travisjbeck/focus-dial/Documents/rendering2.png

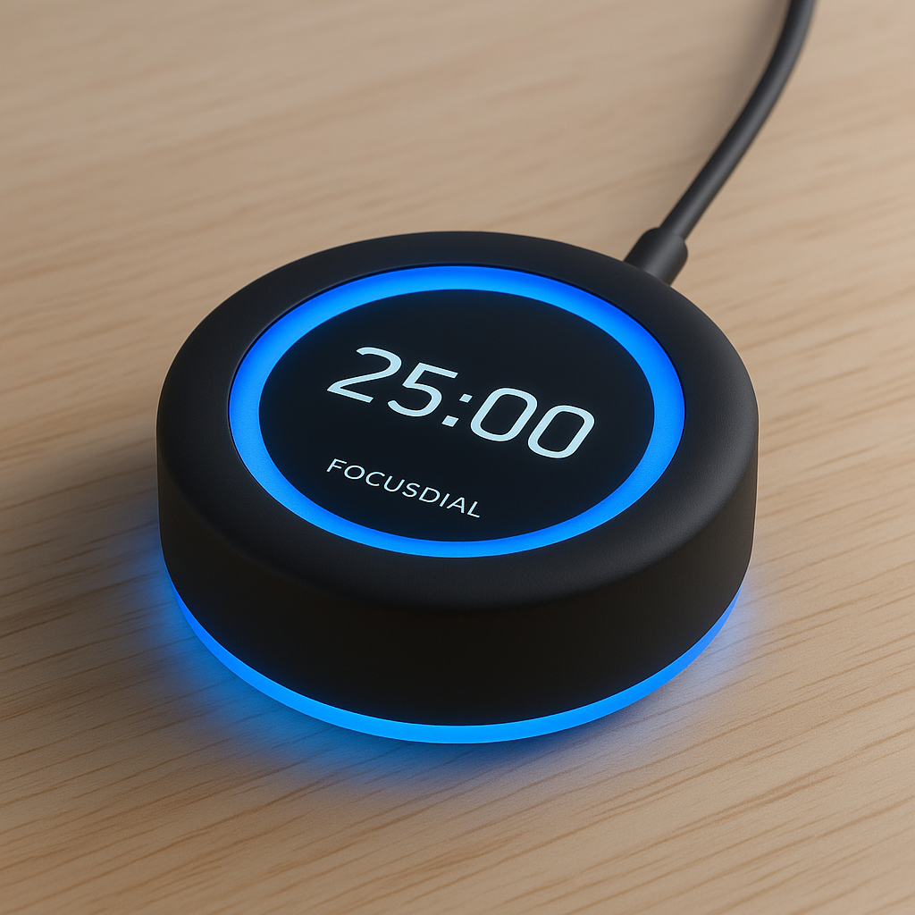
Documents/rendering2.png
