travisjbeck/focus-dial/Documents/rendering3.png

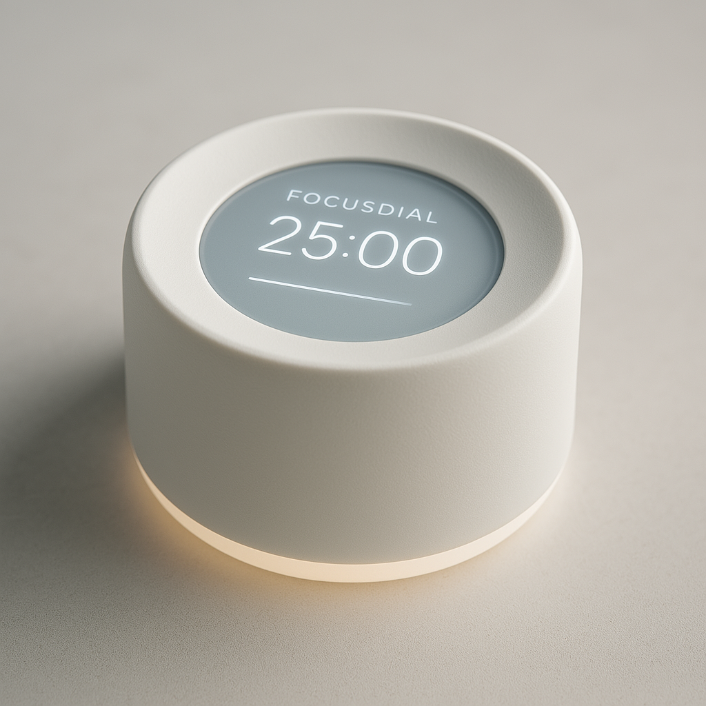
Documents/rendering3.png
