travisjbeck/focus-dial/Documents/rendering4.png

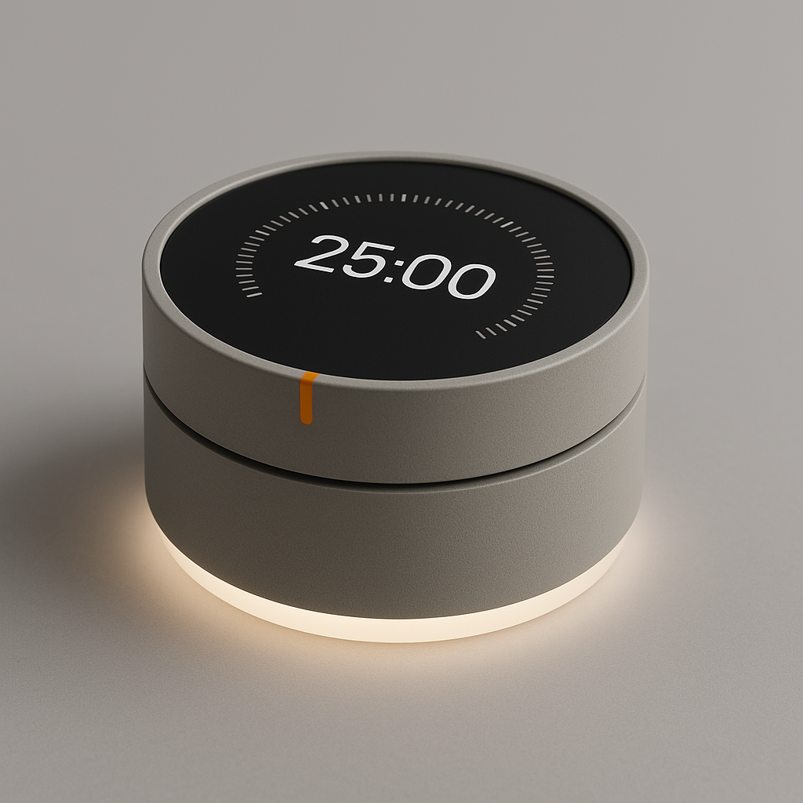
Documents/rendering4.png
