travisjbeck/focus-dial/firmware/idle_screen.png

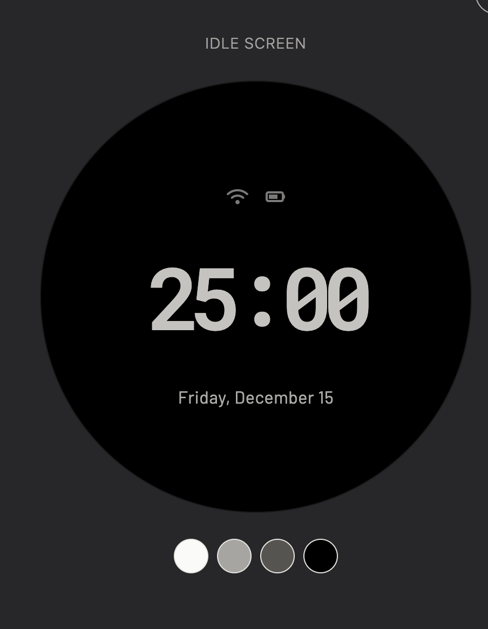
firmware/idle_screen.png
