travisjbeck/focus-dial/firmware/idle_screen_bg_video.png

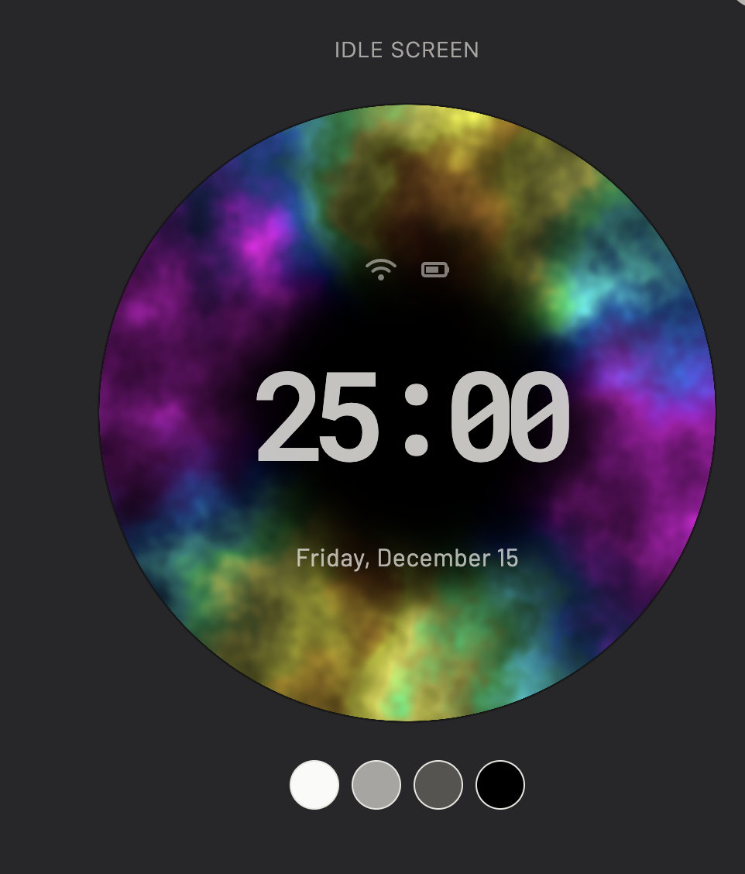
firmware/idle_screen_bg_video.png
