travisjbeck/focus-dial/cad/EVQ-V5B00215B.stp

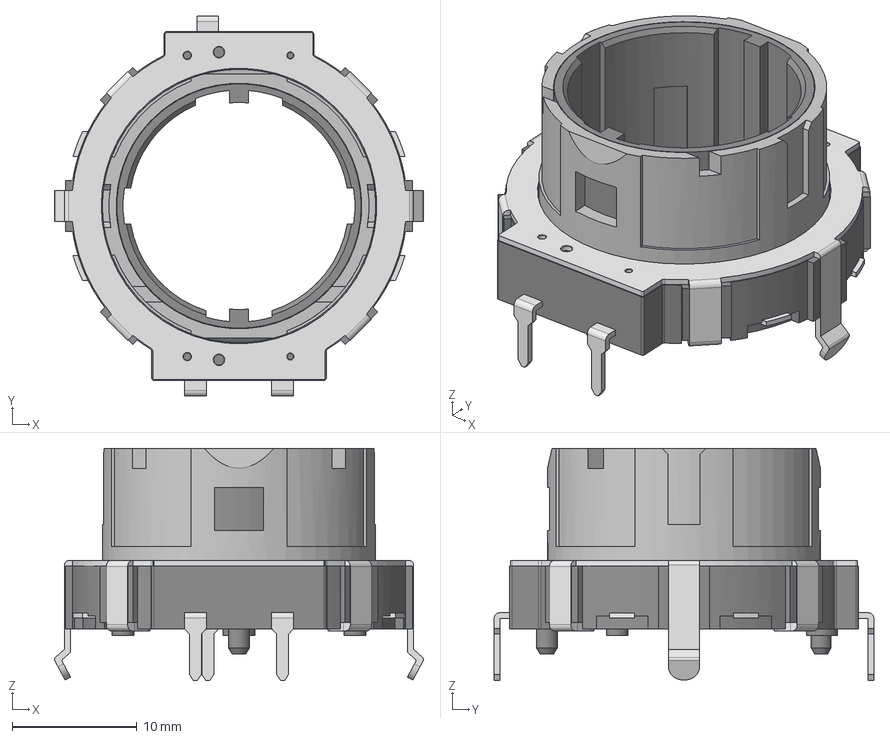
[picture p26: CAD file, 2025-05-12]
cad/EVQ-V5B00215B.stp
29.6 x 30.4 x 18.6 mm
