travisjbeck/focus-dial/cad/STLs/Bezel.stl

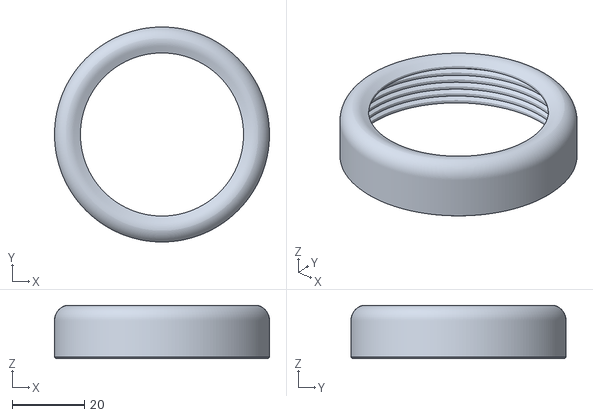
[picture p27: CAD file, 2024-12-27]
cad/STLs/Bezel.stl
59.6 x 59.6 x 14.7
