travisjbeck/focus-dial/cad/PER231-P19-N0010.stp

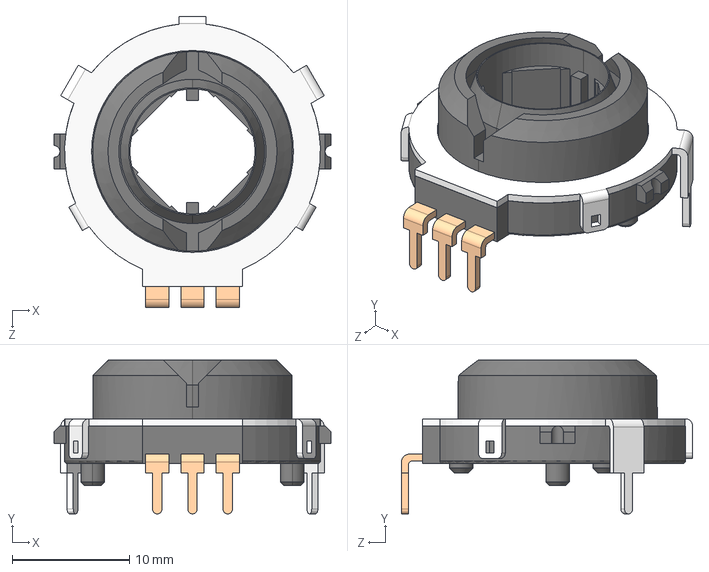
[picture p28: CAD file, 2025-05-12]
cad/PER231-P19-N0010.stp
23.6 x 13.1 x 24.8 mm
