travisjbeck/focus-dial/cad/STLs/Central Ring.stl

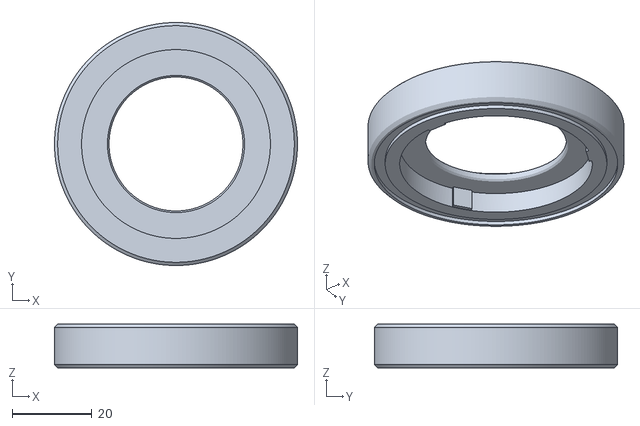
[picture p29: CAD file, 2024-12-27]
cad/STLs/Central Ring.stl
61.0 x 61.0 x 11.0
