travisjbeck/focus-dial/cad/STLs/Encoder Bottom.stl

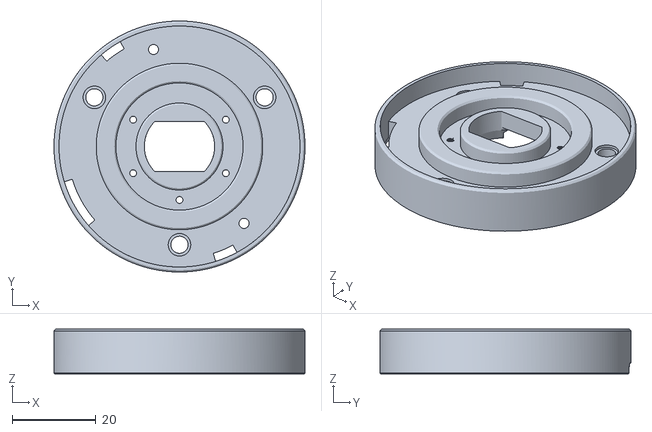
[picture p30: CAD file, 2024-12-27]
cad/STLs/Encoder Bottom.stl
60.0 x 60.0 x 10.7
