travisjbeck/focus-dial/cad/STLs/Button Cap.stl

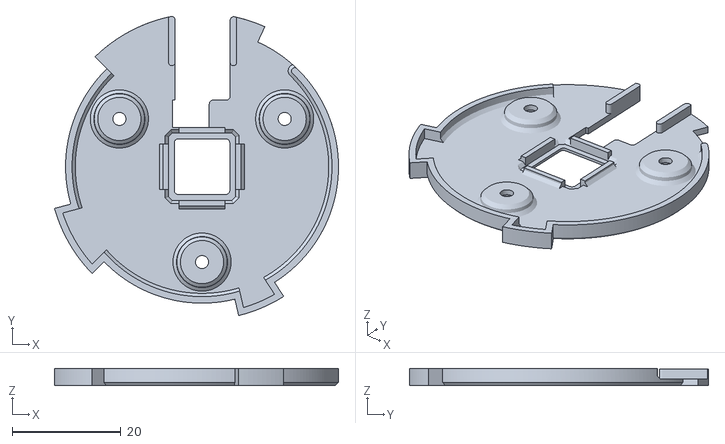
[picture p32: CAD file, 2024-12-27]
cad/STLs/Button Cap.stl
52.2 x 55.0 x 3.20
