travisjbeck/focus-dial/cad/STLs/Screen Backing.stl

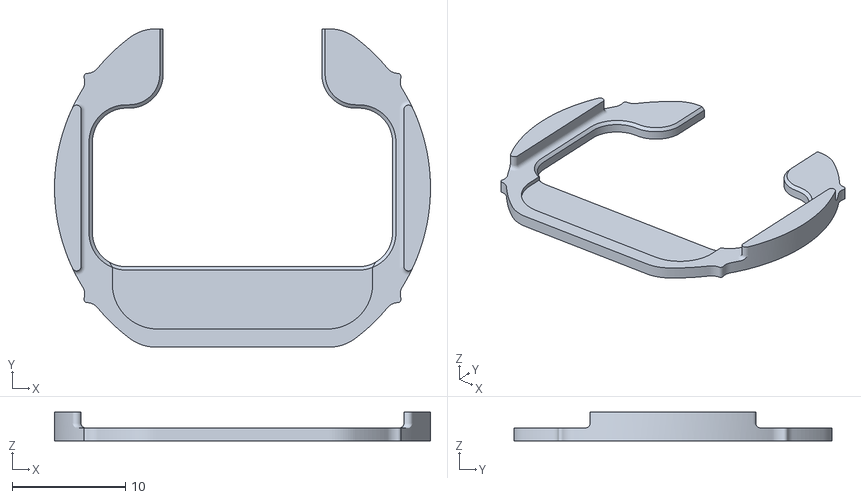
[picture p33: CAD file, 2024-12-27]
cad/STLs/Screen Backing.stl
33.2 x 28.1 x 2.55
