travisjbeck/focus-dial/cad/STLs/Button Holder.stl

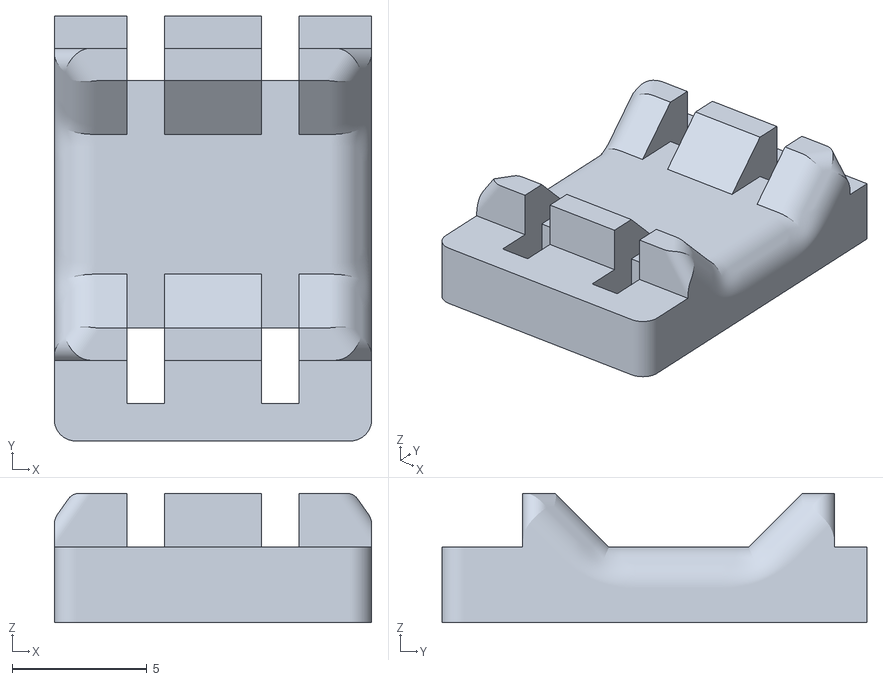
[picture p34: CAD file, 2024-12-27]
cad/STLs/Button Holder.stl
11.8 x 15.8 x 4.81
