travisjbeck/focus-dial/cad/STLs/Central Shaft.stl

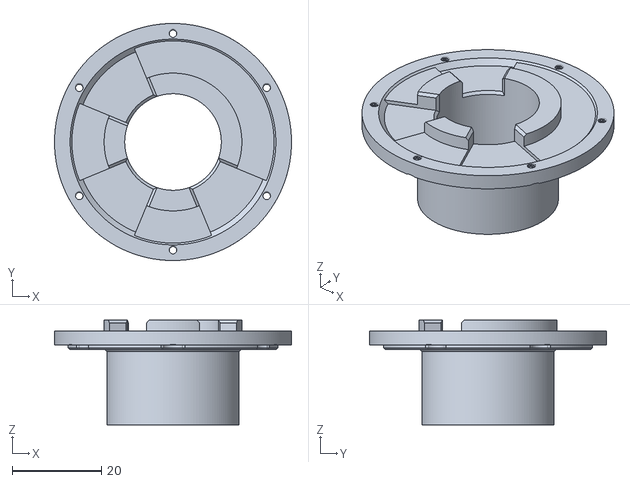
[picture p35: CAD file, 2024-12-27]
cad/STLs/Central Shaft.stl
53.0 x 53.0 x 23.4
