travisjbeck/focus-dial/cad/STLs/Diffuser Mold.stl

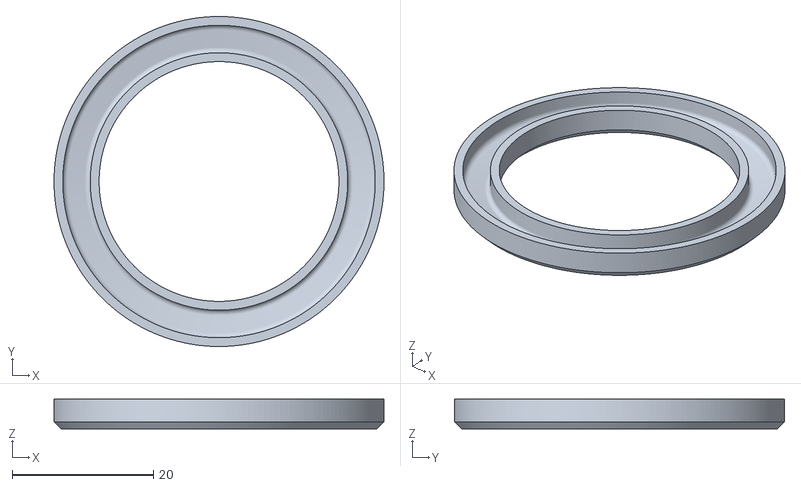
[picture p36: CAD file, 2024-12-27]
cad/STLs/Diffuser Mold.stl
46.8 x 46.8 x 4.20
