travisjbeck/focus-dial/firmware/lv_font_barlow_bold_48.c

/*******************************************************************************
 * Size: 48 px
 * Bpp: 4
 * Opts: --bpp 4 --size 48 --font FONTS/Barlow/Barlow-Bold.ttf -r 0x20-0x7F --format lvgl -o lv_font_barlow_bold_48.c --no-compress --no-prefilter
 ******************************************************************************/

#ifdef LV_LVGL_H_INCLUDE_SIMPLE
#include "lvgl.h"
#else
#include <lvgl.h>
#endif

#ifndef LV_FONT_BARLOW_BOLD_48
#define LV_FONT_BARLOW_BOLD_48 1
#endif

#if LV_FONT_BARLOW_BOLD_48

/*-----------------
 *    BITMAPS
 *----------------*/

/*Store the image of the glyphs*/
static LV_ATTRIBUTE_LARGE_CONST const uint8_t glyph_bitmap[] = {
    /* U+0020 " " */

    /* U+0021 "!" */
    0xe, 0xff, 0xff, 0xf9, 0xf, 0xff, 0xff, 0xfa,
    0xf, 0xff, 0xff, 0xfa, 0xf, 0xff, 0xff, 0xf9,
    0xf, 0xff, 0xff, 0xf9, 0xe, 0xff, 0xff, 0xf8,
    0xe, 0xff, 0xff, 0xf8, 0xd, 0xff, 0xff, 0xf7,
    0xd, 0xff, 0xff, 0xf7, 0xc, 0xff, 0xff, 0xf6,
    0xc, 0xff, 0xff, 0xf5, 0xb, 0xff, 0xff, 0xf5,
    0xb, 0xff, 0xff, 0xf4, 0xa, 0xff, 0xff, 0xf4,
    0xa, 0xff, 0xff, 0xf3, 0x9, 0xff, 0xff, 0xf3,
    0x9, 0xff, 0xff, 0xf2, 0x8, 0xff, 0xff, 0xf1,
    0x8, 0xff, 0xff, 0xf1, 0x7, 0xff, 0xff, 0xf0,
    0x7, 0xff, 0xff, 0xf0, 0x5, 0xff, 0xff, 0xe0,
    0x0, 0x0, 0x0, 0x0, 0x0, 0x0, 0x0, 0x0,
    0x0, 0x0, 0x0, 0x0, 0x0, 0x0, 0x0, 0x0,
    0x0, 0x48, 0x84, 0x0, 0xa, 0xff, 0xff, 0xa0,
    0x6f, 0xff, 0xff, 0xf6, 0xbf, 0xff, 0xff, 0xfb,
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
    0x5f, 0xff, 0xff, 0xf6, 0xe, 0xff, 0xff, 0xfd,
    0x0, 0x0, 0x0, 0x5, 0xff, 0xff, 0xff, 0x60,
    0xef, 0xff, 0xff, 0xe0, 0x0, 0x0, 0x0, 0x7f,
    0xff, 0xff, 0xf6, 0xd, 0xff, 0xff, 0xff, 0x60,
    0x0, 0x0, 0xe, 0xff, 0xff, 0xff, 0x50, 0xaf,
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
